MintyTrebor/QRPlay/media/PXL_20241117_133520910.jpg

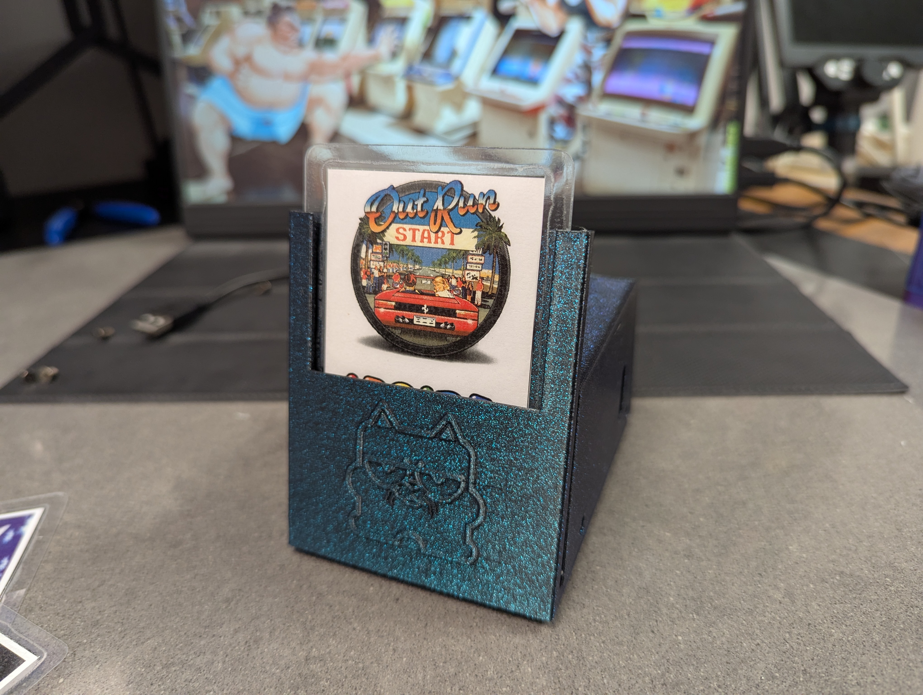
media/PXL_20241117_133520910.jpg
