MintyTrebor/QRPlay/media/PXL_20241117_150625066.jpg

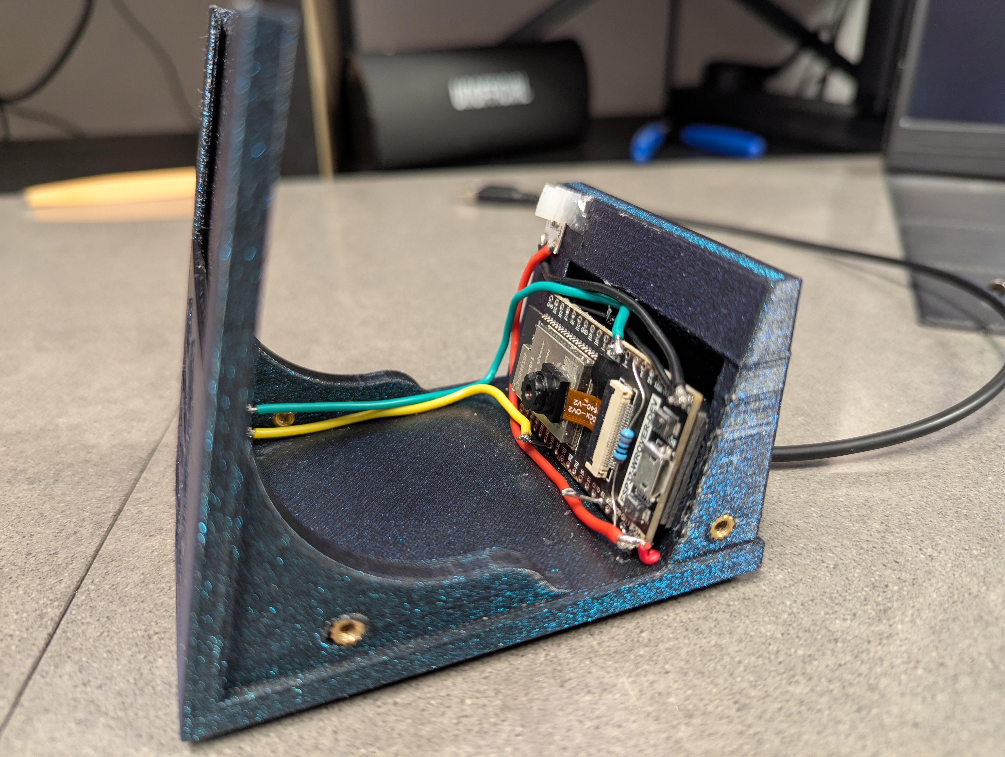
media/PXL_20241117_150625066.jpg
